cmarrin/PostLightController/NeoPixel.h

/*-------------------------------------------------------------------------
This source file is a part of mil

For the latest info, see http://www.marrin.org/

Copyright (c) 2025, Chris Marrin
All rights reserved.
-------------------------------------------------------------------------*/

// Wrapper around Adafruit NeoPixel driver

#pragma once

#include <cstdint>
#include <cstdio>

#if defined ARDUINO
#include <Adafruit_NeoPixel.h>
#endif

namespace mil {

#if defined ARDUINO

class NeoPixel
{
public:
    NeoPixel(uint16_t numPixels, uint8_t ledPin) : _pixels(numPixels, ledPin, NEO_GRB + NEO_KHZ800) { }

    void begin() { _pixels.begin(); }
    void setBrightness(uint8_t b) { _pixels.setBrightness(b); }
    uint16_t numPixels() const { return _pixels.numPixels(); }
    void show() { _pixels.show(); }
    
    void setLight(uint16_t i, uint32_t color)
    {
        _pixels.setPixelColor(i, color);
    }
    
    void setLights(uint16_t from, uint16_t count, uint32_t color)
    {
        for (int i = 0; i < count; ++i) {
            _pixels.setPixelColor(from + i, color);
        }
    }
    
    uint32_t color(uint8_t h, uint8_t s, uint8_t v) { return Adafruit_NeoPixel::gamma32(Adafruit_NeoPixel::ColorHSV(uint16_t(h) * 256, s, v)); }

private:
    Adafruit_NeoPixel _pixels;
};

#elif defined ESP_PLATFORM

class NeoPixel
{
public:
    NeoPixel(uint16_t numPixels, uint8_t ledPin) : _numPixels(numPixels) { }

    void begin() { }
    void setBrightness(uint8_t b) { }
    uint16_t numPixels() const { return _numPixels; }
    void show() { }
    
    void setLight(uint16_t i, uint32_t color)
    {
        printf("setLight(%d, 0x%08x)\n", i, (unsigned int) color);
    }

    void setLights(uint16_t from, uint16_t count, uint32_t color)
    {
        printf("setLights(%d, %d, 0x%08x)\n", from, count, (unsigned int) color);
    }

    uint32_t color(uint8_t h, uint8_t s, uint8_t v) { return (uint32_t(h) << 16) | (uint32_t(s) << 8) | uint32_t(v); }

  private:
    uint16_t _numPixels = 0;
};

#else

class NeoPixel
{
public:
    NeoPixel(uint16_t numPixels, uint8_t ledPin) : _numPixels(numPixels) { }

    void begin() { }
    void setBrightness(uint8_t b) { }
    uint16_t numPixels() const { return _numPixels; }
    void show() { }
    
    void setLight(uint16_t i, uint32_t color)
    {
        printf("setLight(%d, 0x%08x)\n", i, color);
    }

    void setLights(uint16_t from, uint16_t count, uint32_t color)
    {
        printf("setLights(%d, %d, 0x%08x)\n", from, count, color);
    }

    uint32_t color(uint8_t h, uint8_t s, uint8_t v) { return (uint32_t(h) << 16) | (uint32_t(s) << 8) | uint32_t(v); }

  private:
    uint16_t _numPixels = 0;
};

#endif

}
